fhessel/smartpeg/experiments/2017-11-20-experiment03.csv

sensor | time_ms | humidity_percent | temperature_degc | dryness_raw
DHT22 | 56170 | 54.400002 | 21.600000 | 28.739002
DHT22 | 56671 | 54.400002 | 21.600000 | 29.130011
DHT22 | 57172 | 54.400002 | 21.600000 | 29.716520
DHT22 | 57673 | 54.400002 | 21.700001 | 18.866079
DHT22 | 58449 | 54.400002 | 21.700001 | 26.001955
DHT22 | 58950 | 54.400002 | 21.700001 | 28.152493
DHT22 | 59451 | 54.400002 | 21.700001 | 28.445747
DHT22 | 59952 | 54.400002 | 21.600000 | 3.910069
DHT22 | 60727 | 54.400002 | 21.600000 | 9.775171
DHT22 | 61228 | 54.400002 | 21.600000 | 14.956012
DHT22 | 61729 | 54.400002 | 21.600000 | 22.776148
DHT22 | 62230 | 54.299999 | 21.600000 | 27.663734
DHT22 | 63006 | 54.299999 | 21.600000 | 1.857283
DHT22 | 63507 | 54.299999 | 21.600000 | 3.910069
DHT22 | 64008 | 54.299999 | 21.600000 | 10.166178
DHT22 | 64509 | 54.299999 | 21.700001 | 28.445747
DHT22 | 65285 | 54.299999 | 21.700001 | 28.445747
DHT22 | 65786 | 54.299999 | 21.700001 | 6.256110
DHT22 | 66287 | 54.299999 | 21.700001 | 1.955034
DHT22 | 66788 | 54.200001 | 21.600000 | 28.836754
DHT22 | 67564 | 54.200001 | 21.600000 | 28.445747
DHT22 | 68065 | 54.200001 | 21.600000 | 28.543499
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
