fhessel/smartpeg/experiments/2017-11-25-experiment04.csv

sensor | time_ms | humidity_percent | temperature_degc | dryness_raw
DHC1080 | 55261 | 68.164062 | 23.627319 | 62.365593
DHT22 | 55261 | 69.300003 | 22.500000 | 62.365593
DHC1080 | 60538 | 68.164062 | 23.627319 | 58.455524
DHT22 | 60538 | 69.000000 | 22.400000 | 58.455524
DHC1080 | 65814 | 68.164062 | 23.627319 | 55.034214
DHT22 | 65814 | 69.199997 | 22.400000 | 55.034214
DHC1080 | 71090 | 68.164062 | 23.627319 | 64.125122
DHT22 | 71090 | 69.500000 | 22.299999 | 64.125122
DHC1080 | 76366 | 69.494629 | 23.425903 | 66.471161
DHT22 | 76366 | 70.000000 | 22.299999 | 66.471161
DHC1080 | 81643 | 69.494629 | 23.425903 | 72.043015
DHT22 | 81643 | 69.500000 | 22.200001 | 72.043015
DHC1080 | 86919 | 69.494629 | 23.425903 | 61.681328
DHT22 | 86919 | 69.500000 | 22.200001 | 61.681328
DHC1080 | 92195 | 69.494629 | 23.425903 | 58.064518
DHT22 | 92195 | 69.500000 | 22.100000 | 58.064518
DHC1080 | 97471 | 70.623779 | 23.305054 | 54.349953
DHT22 | 97471 | 69.500000 | 22.100000 | 54.349953
DHC1080 | 102748 | 70.623779 | 23.305054 | 63.636364
DHT22 | 102748 | 69.900002 | 22.100000 | 63.636364
DHC1080 | 108024 | 70.623779 | 23.305054 | 72.629524
DHT22 | 108024 | 70.099998 | 22.100000 | 72.629524
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
