fhessel/smartpeg/hardware/code/config/pins.h

/*
 * pins.h
 *
 *  Created on: Nov 14, 2017
 *      Author: frank
 */

#ifndef CONFIG_PINS_H_
#define CONFIG_PINS_H_

// Required for access to pin constants
#include "Arduino.h"

// Status LED for WiFi connection
#define PIN_LED_WIFI    D5

// Peg sensor
#define PIN_PEG         A0

// DHT sensor
#define PIN_DHT22       D6

#endif /* CONFIG_PINS_H_ */
