fhessel/smartpeg/hardware/code/config/wificonfig.h

/*
 * wificonfig.h
 *
 *  Created on: Nov 14, 2017
 *      Author: frank
 */

#ifndef CONFIG_WIFICONFIG_H_
#define CONFIG_WIFICONFIG_H_

const char* WIFI_SSID = (const char*)"<insert ssid here>";
const char* WIFI_PSK  = (const char*)"<insert pre shared key here>";



#endif /* CONFIG_WIFICONFIG_H_ */
